lutetjeff/popn2/production/sl120.dxf

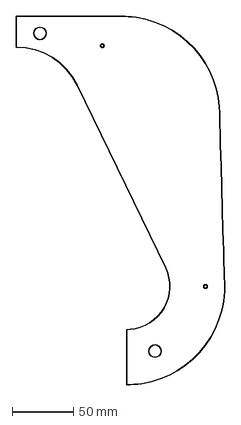
[picture p19: CAD file, 2026-04-07]
production/sl120.dxf
169.7 x 300.0 mm
