lutetjeff/popn2/production/sl80.dxf

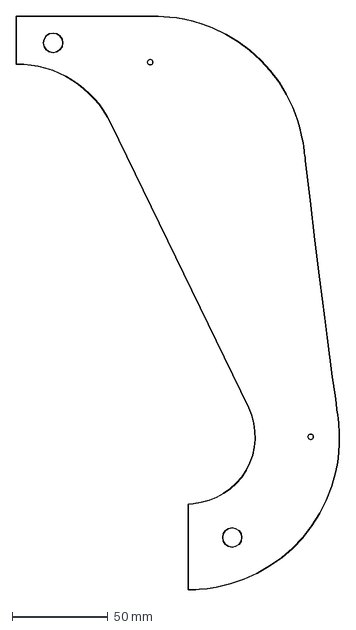
[picture p20: CAD file, 2026-04-07]
production/sl80.dxf
169.2 x 300.0 mm
