lutetjeff/popn2/production/top.dxf

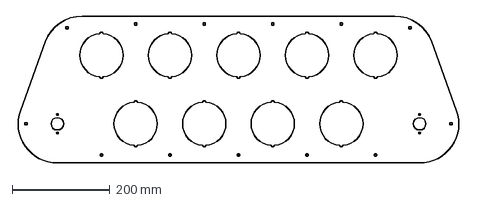
[picture p21: CAD file, 2026-04-07]
production/top.dxf
908.2 x 300.0 mm
