lutetjeff/popn2/production/sl122.dxf

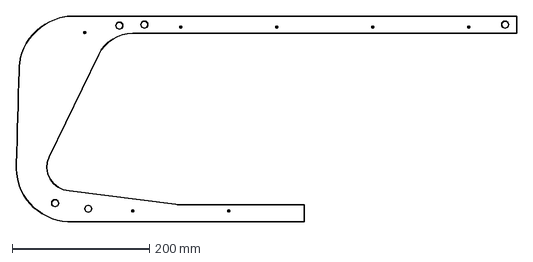
[picture p22: CAD file, 2026-04-07]
production/sl122.dxf
729.8 x 300.0 mm
