lutetjeff/popn2/production/sl130.dxf

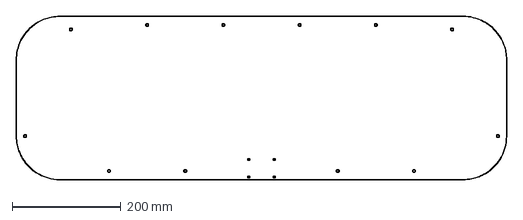
[picture p23: CAD file, 2026-04-07]
production/sl130.dxf
900.0 x 300.0 mm
