lutetjeff/popn2/production/sl110.dxf

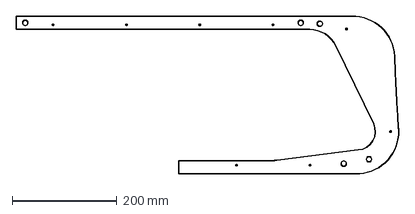
[picture p24: CAD file, 2026-04-07]
production/sl110.dxf
729.6 x 300.0 mm
