lutetjeff/popn2/production/sl91.dxf

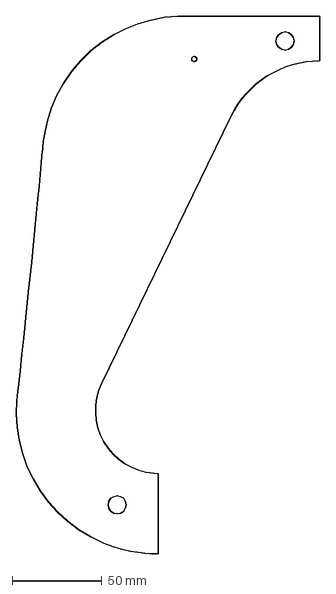
[picture p25: CAD file, 2026-04-07]
production/sl91.dxf
169.1 x 300.0 mm
