lutetjeff/popn2/production/sl121.dxf

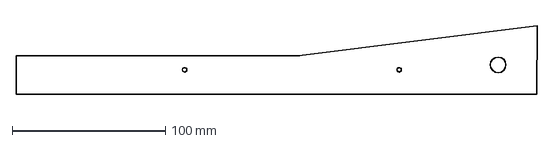
[picture p26: CAD file, 2026-04-07]
production/sl121.dxf
340.0 x 44.8 mm
