lutetjeff/popn2/production/sl41.dxf

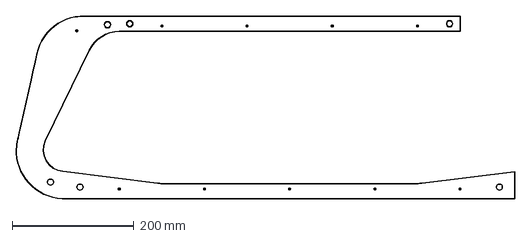
[picture p27: CAD file, 2026-04-07]
production/sl41.dxf
819.4 x 300.0 mm
