lutetjeff/popn2/production/sl00.dxf

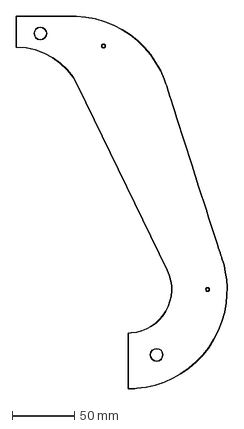
[picture p28: CAD file, 2026-04-07]
production/sl00.dxf
170.0 x 300.0 mm
