lutetjeff/popn2/production/sl21.dxf

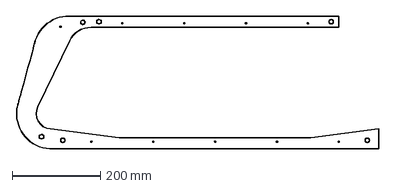
[picture p29: CAD file, 2026-04-07]
production/sl21.dxf
819.7 x 300.0 mm
