lutetjeff/popn2/production/sl10.dxf

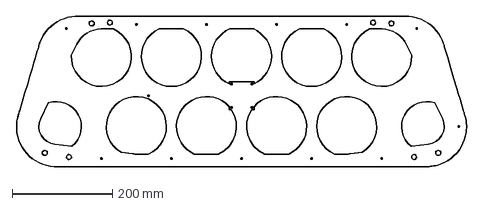
[picture p30: CAD file, 2026-04-07]
production/sl10.dxf
899.4 x 300.0 mm
