lutetjeff/popn2/production/sl50.dxf

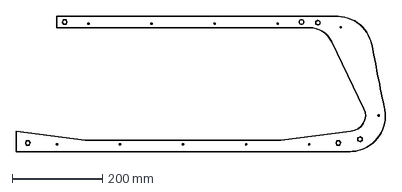
[picture p31: CAD file, 2026-04-07]
production/sl50.dxf
819.5 x 300.0 mm
