lutetjeff/popn2/production/sl30.dxf

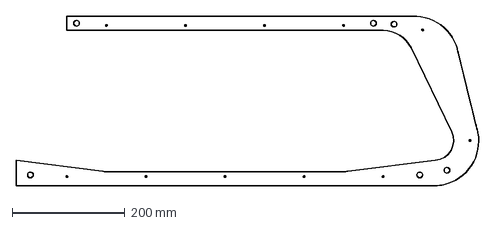
[picture p32: CAD file, 2026-04-07]
production/sl30.dxf
819.6 x 300.0 mm
