lutetjeff/popn2/production/sl90.dxf

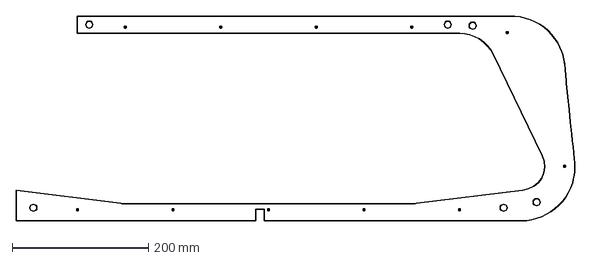
[picture p33: CAD file, 2026-04-07]
production/sl90.dxf
819.2 x 300.0 mm
