lutetjeff/popn2/production/sl101.dxf

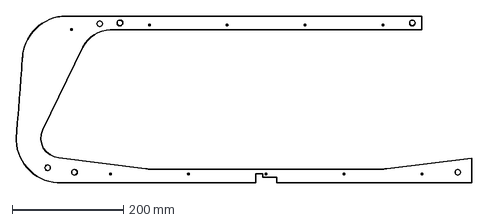
[picture p34: CAD file, 2026-04-07]
production/sl101.dxf
819.7 x 300.0 mm
