lutetjeff/popn2/production/sl40.dxf

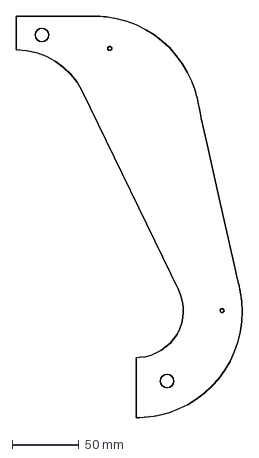
[picture p35: CAD file, 2026-04-07]
production/sl40.dxf
169.6 x 300.0 mm
