lutetjeff/popn2/production/sl20.dxf

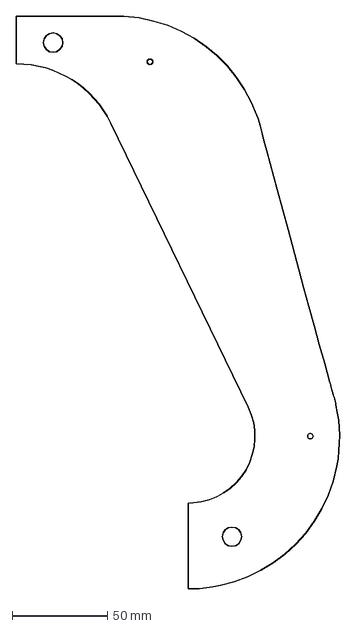
[picture p36: CAD file, 2026-04-07]
production/sl20.dxf
169.4 x 300.0 mm
