lutetjeff/popn2/production/sl60.dxf

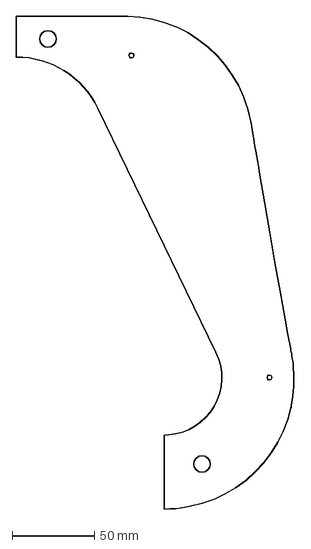
[picture p37: CAD file, 2026-04-07]
production/sl60.dxf
169.4 x 300.0 mm
