lutetjeff/popn2/production/sl111.dxf

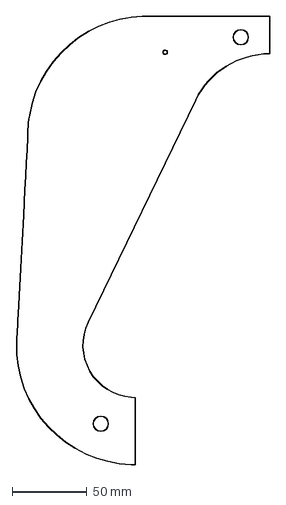
[picture p38: CAD file, 2026-04-07]
production/sl111.dxf
169.6 x 300.0 mm
