lutetjeff/popn2/production/sl71.dxf

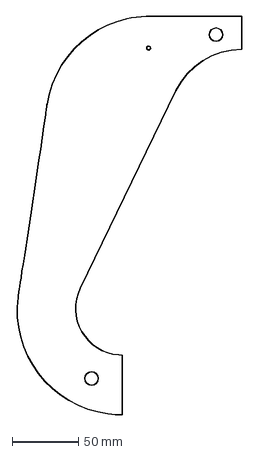
[picture p39: CAD file, 2026-04-07]
production/sl71.dxf
169.7 x 300.0 mm
