lutetjeff/popn2/production/sl81.dxf

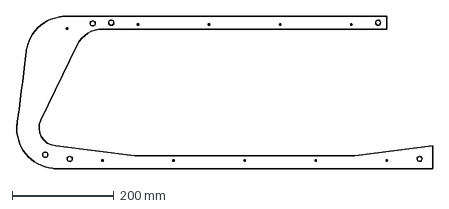
[picture p40: CAD file, 2026-04-07]
production/sl81.dxf
819.6 x 300.0 mm
