lutetjeff/popn2/production/foam.dxf

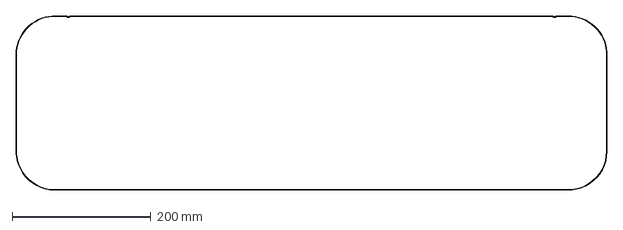
[picture p41: CAD file, 2026-04-07]
production/foam.dxf
850.0 x 250.0 mm
