lutetjeff/popn2/production/sl61.dxf

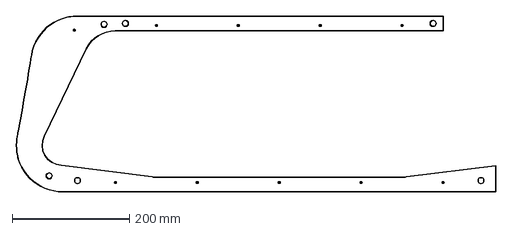
[picture p42: CAD file, 2026-04-07]
production/sl61.dxf
819.4 x 300.1 mm
