lutetjeff/popn2/production/sl31.dxf

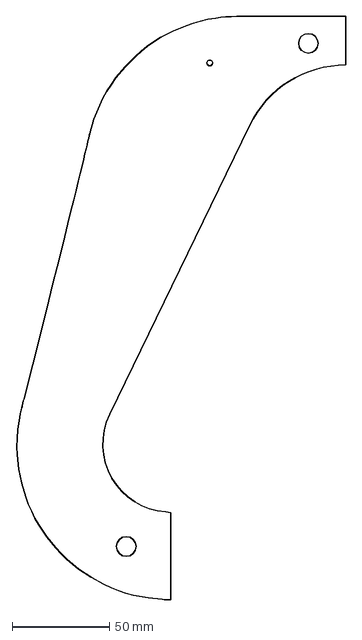
[picture p43: CAD file, 2026-04-07]
production/sl31.dxf
169.6 x 300.0 mm
